Nauman3S/Operational-Equipment-EfficiencySensing/Circuit/Circuit_bb.png

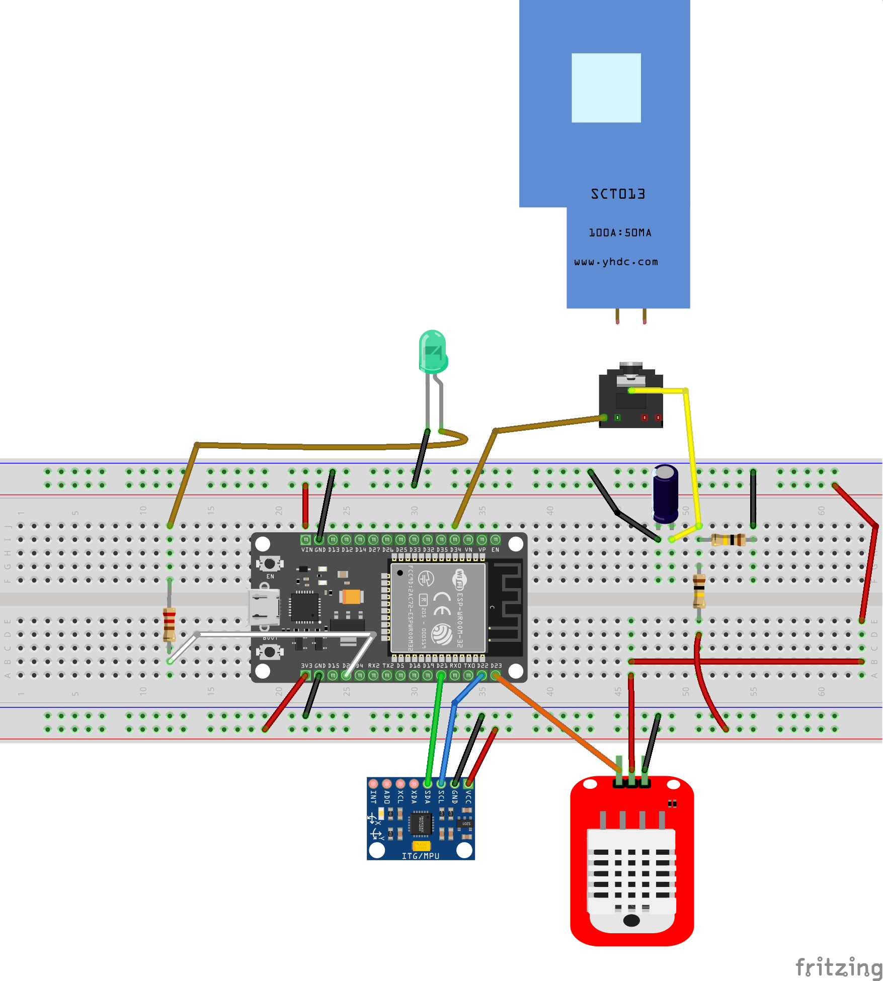
Circuit/Circuit_bb.png
