Nauman3S/Operational-Equipment-EfficiencySensing/Circuit/scr3.png

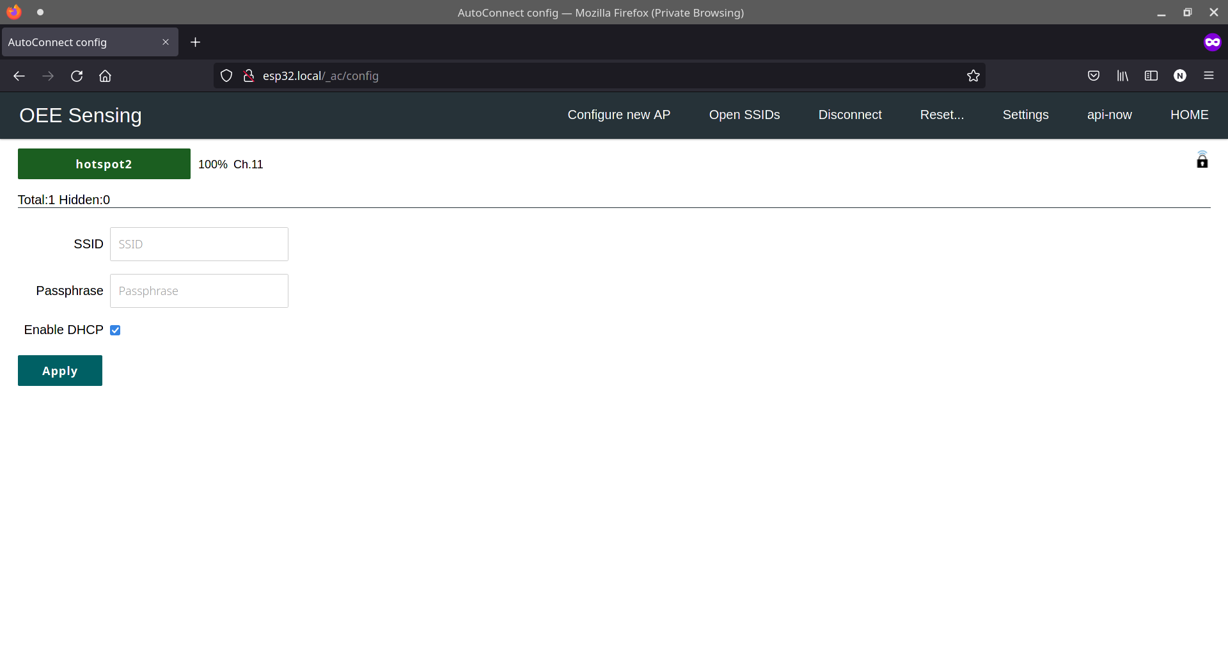
Circuit/scr3.png
