Nauman3S/Operational-Equipment-EfficiencySensing/Circuit/scr5.png

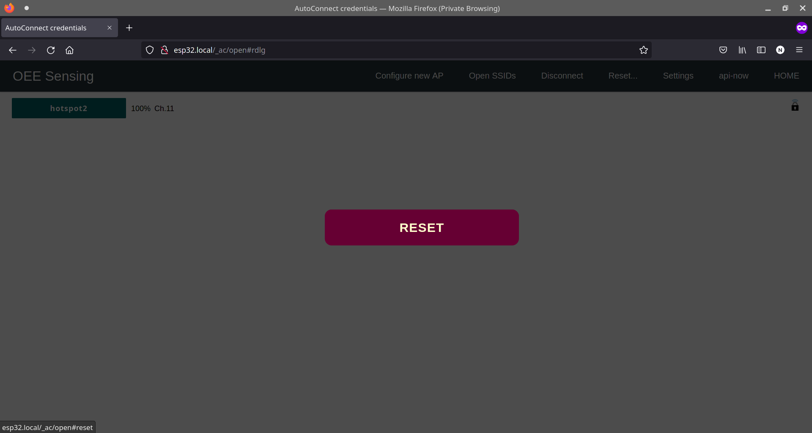
Circuit/scr5.png
