Nauman3S/Operational-Equipment-EfficiencySensing/Circuit/scr6.png

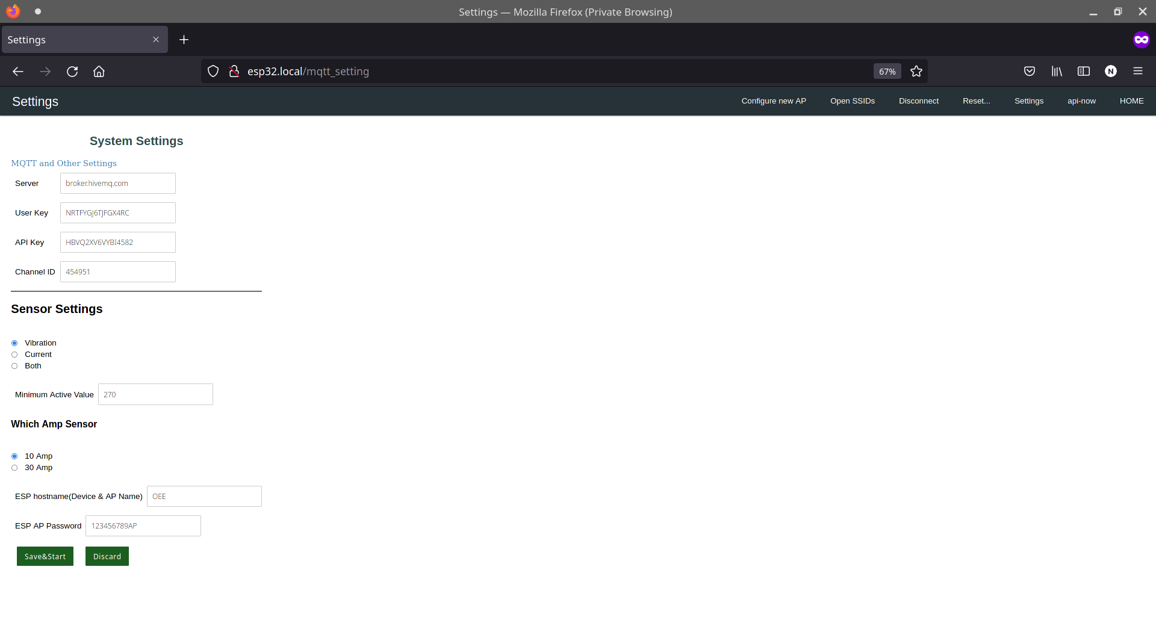
Circuit/scr6.png
