Nauman3S/Operational-Equipment-EfficiencySensing/Circuit/scr8.png

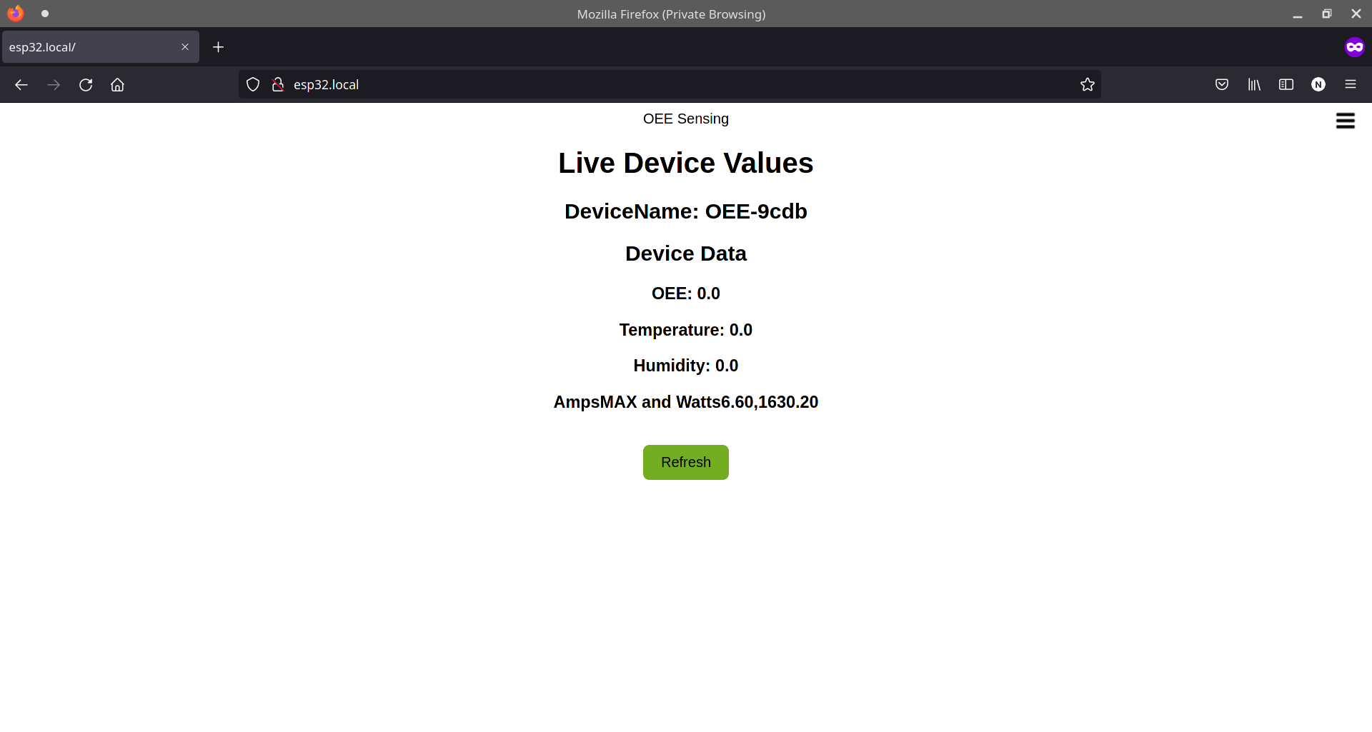
Circuit/scr8.png
