Nauman3S/Operational-Equipment-EfficiencySensing/Circuit/scr10.png

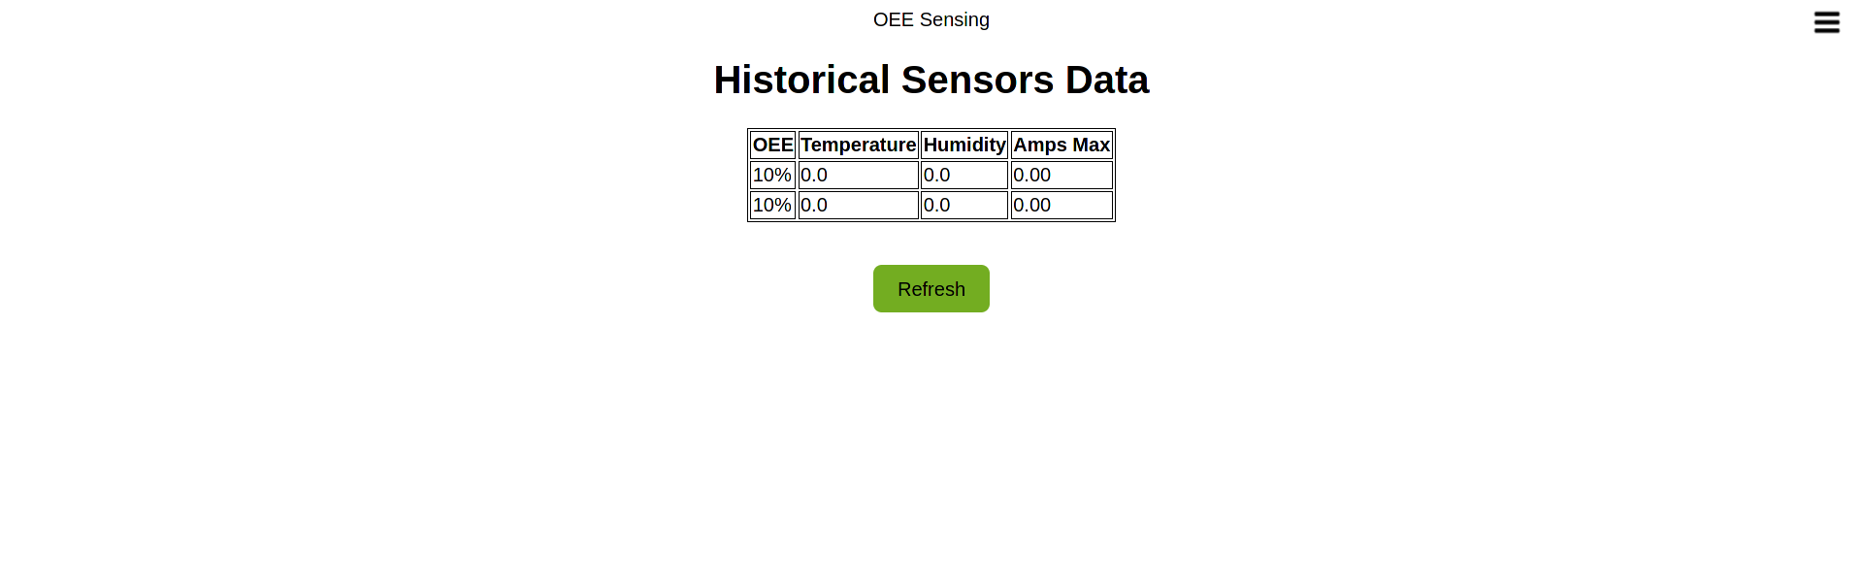
Circuit/scr10.png
