Nauman3S/Operational-Equipment-EfficiencySensing/Circuit/sctWiring.jpg

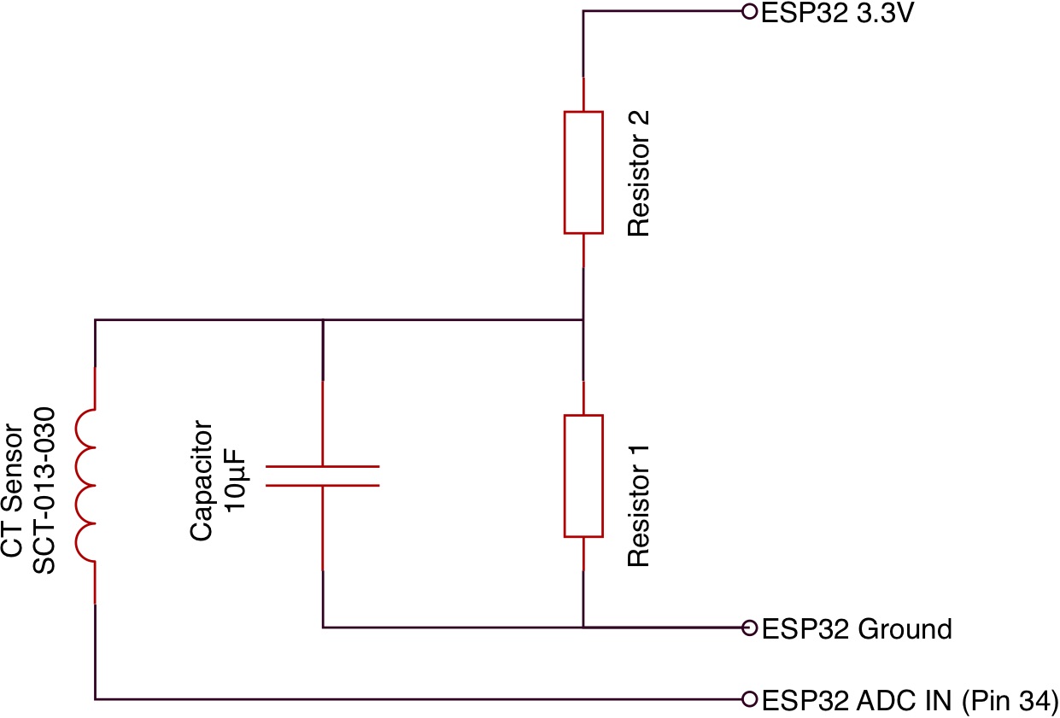
Circuit/sctWiring.jpg
