Nauman3S/Operational-Equipment-EfficiencySensing/Firmware/dhtHandler.h

// DHT Temperature & Humidity Sensor
// Unified Sensor Library Example
// Written by Tony DiCola for Adafruit Industries
// Released under an MIT license.

// REQUIRES the following Arduino libraries:
// - DHT Sensor Library: https://github.com/adafruit/DHT-sensor-library
// - Adafruit Unified Sensor Lib: https://github.com/adafruit/Adafruit_Sensor

#include <Adafruit_Sensor.h>
#include <DHT.h>
#include <DHT_U.h>

#define DHTPIN 23 // Digital pin connected to the DHT sensor
// Feather HUZZAH ESP8266 note: use pins 3, 4, 5, 12, 13 or 14 --
// Pin 15 can work but DHT must be disconnected during program upload.

// Uncomment the type of sensor in use:
//#define DHTTYPE    DHT11     // DHT 11
#define DHTTYPE DHT22 // DHT 22 (AM2302)
//#define DHTTYPE    DHT21     // DHT 21 (AM2301)

// See guide for details on sensor wiring and usage:
//   https://learn.adafruit.com/dht/overview

DHT_Unified dht(DHTPIN, DHTTYPE);

uint32_t delayMS;
float convertCtoF(float c) { return c * 1.8 + 32; }

void setupDHT22()
{

    // Initialize device.
    dht.begin();
    Serial.println(F("DHTxx Unified Sensor"));
    // Print temperature sensor details.
    sensor_t sensor;
    dht.temperature().getSensor(&sensor);
    Serial.println(F("------------------------------------"));
    Serial.println(F("Temperature Sensor"));
    Serial.print(F("Sensor Type: "));
    Serial.println(sensor.name);
    Serial.print(F("Driver Ver:  "));
    Serial.println(sensor.version);
    Serial.print(F("Unique ID:   "));
    Serial.println(sensor.sensor_id);
    Serial.print(F("Max Value:   "));
    Serial.print(sensor.max_value);
    Serial.println(F("°C"));
    Serial.print(F("Min Value:   "));
    Serial.print(sensor.min_value);
    Serial.println(F("°C"));
    Serial.print(F("Resolution:  "));
    Serial.print(sensor.resolution);
    Serial.println(F("°C"));
    Serial.println(F("------------------------------------"));
    // Print humidity sensor details.
    dht.humidity().getSensor(&sensor);
    Serial.println(F("Humidity Sensor"));
    Serial.print(F("Sensor Type: "));
    Serial.println(sensor.name);
    Serial.print(F("Driver Ver:  "));
    Serial.println(sensor.version);
    Serial.print(F("Unique ID:   "));
    Serial.println(sensor.sensor_id);
    Serial.print(F("Max Value:   "));
    Serial.print(sensor.max_value);
    Serial.println(F("%"));
    Serial.print(F("Min Value:   "));
    Serial.print(sensor.min_value);
    Serial.println(F("%"));
    Serial.print(F("Resolution:  "));
    Serial.print(sensor.resolution);
    Serial.println(F("%"));
    Serial.println(F("------------------------------------"));
    // Set delay between sensor readings based on sensor details.
    delayMS = sensor.min_delay / 1000;
}

String getTemp(String unit)
{
    String data = "";
    // Get temperature event and print its value.
    sensors_event_t event;
    dht.temperature().getEvent(&event);

    if (isnan(event.temperature))
    {
        Serial.println(F("Error reading temperature!"));
        data = String("0.0");
        return data;
    }
    if (unit == "C")
    {
        data = String(event.temperature);
    }
    else if (unit == "F")
    {
        data = String(convertCtoF(event.temperature));
    }
    return data;
}
String getHumid()
{
    String data = "";
    // Get temperature event and print its value.
    sensors_event_t event;
    dht.humidity().getEvent(&event);
    if (isnan(event.relative_humidity))
    {
        Serial.println(F("Error reading Humidity!"));
        data = String("0.0");
        return data;
    }
    data = String(event.relative_humidity);
    return data;
}
String getTempHumid(String unit)
{
    // Delay between measurements.
    //delay(10);
    String data = "";
    // Get temperature event and print its value.
    sensors_event_t event;
    dht.temperature().getEvent(&event);
    if (isnan(event.temperature))
    {
        Serial.println(F("Error reading temperature!"));
        data = String("0.0") + String(",") + String("0%");
        return data;
    }
    else
    {
        Serial.print(F("Temperature: "));
        Serial.print(event.temperature);
        if (unit == "C")
        {
            data = String(event.temperature);
        }
        else if (unit == "F")
        {
            data = String(convertCtoF(event.temperature));
        }

        Serial.println(F("°C"));
    }
    // Get humidity event and print its value.
    dht.humidity().getEvent(&event);
    if (isnan(event.relative_humidity))
    {
        Serial.println(F("Error reading humidity!"));
    }
    else
    {
        Serial.print(F("Humidity: "));
        Serial.print(event.relative_humidity);
        data = data + String(",") + String(event.relative_humidity);
        Serial.println(F("%"));
    }
    return data;
}
